Icecovery/CSI4103-Project-W2022/Asset/test_images/Eillpes.jpg

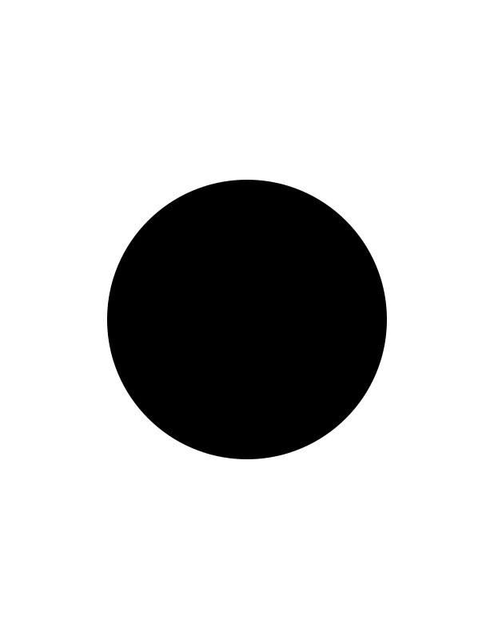
Asset/test_images/Eillpes.jpg
