Icecovery/CSI4103-Project-W2022/Asset/test_images/Grid.jpg

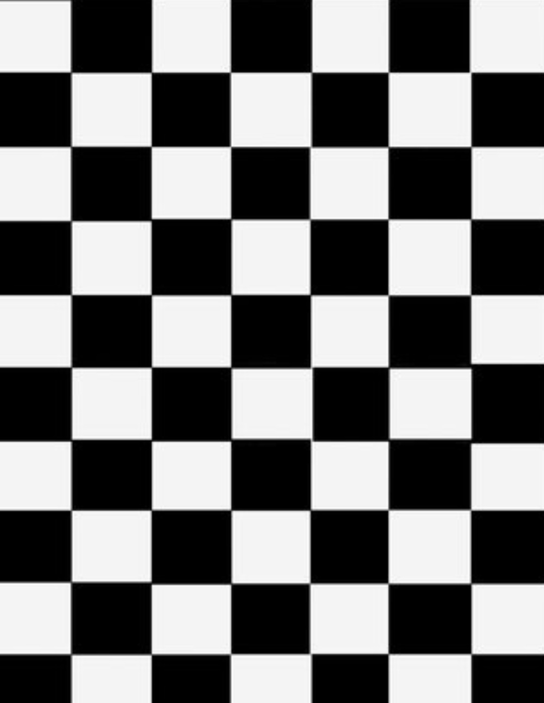
Asset/test_images/Grid.jpg
